zach401/Solaris_MPPT/Electrical Hardware/BoardReference.png

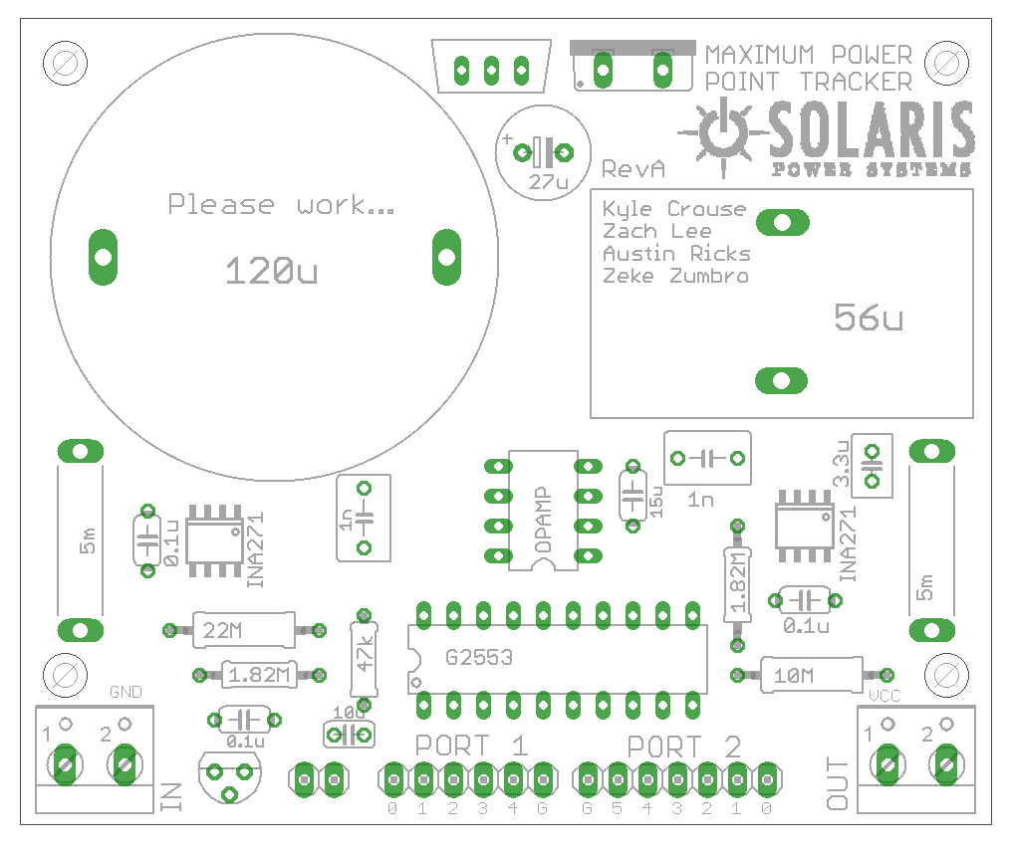
Electrical Hardware/BoardReference.png
