zach401/Solaris_MPPT/Electrical Hardware/DC-DC Converter/DC-DC Schem.PNG

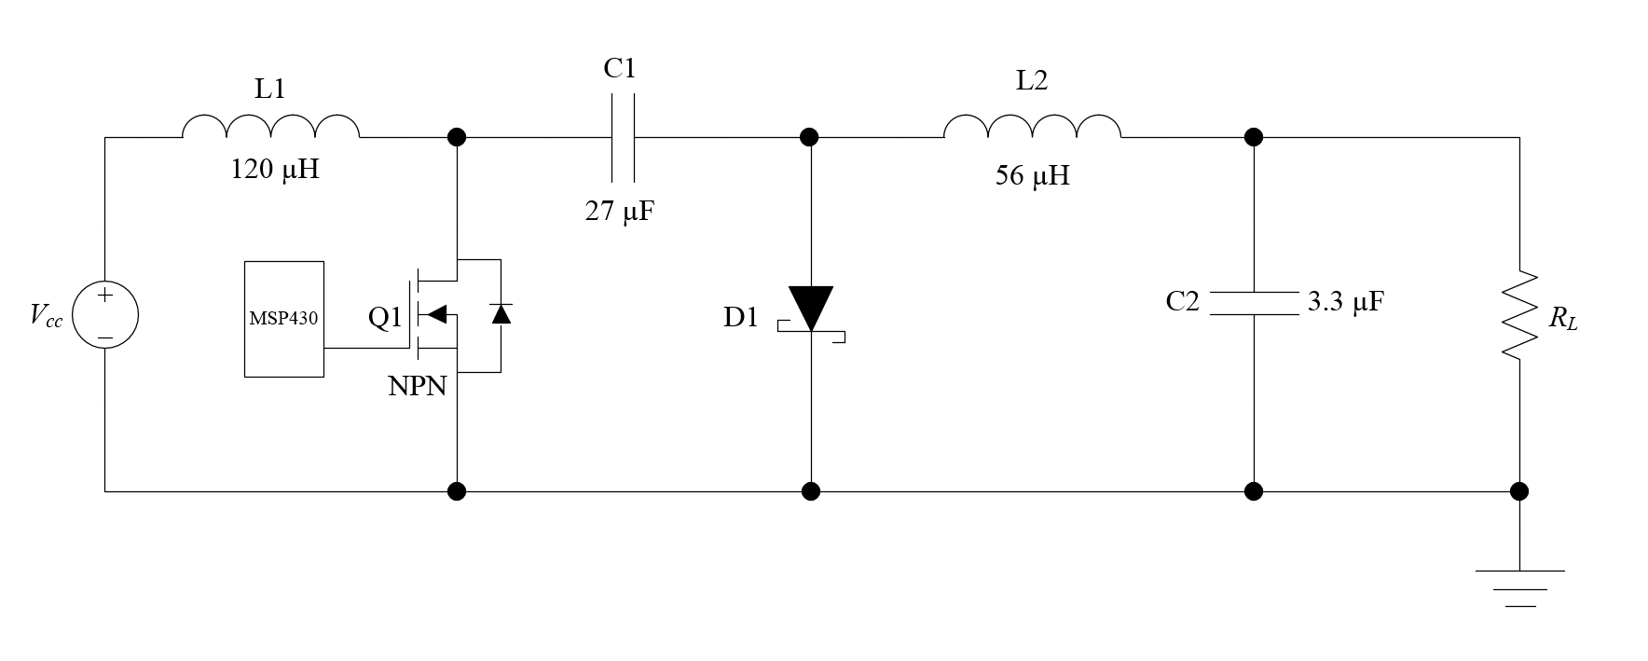
Electrical Hardware/DC-DC Converter/DC-DC Schem.PNG
