zach401/Solaris_MPPT/Electrical Hardware/EAGLE/Capture.PNG

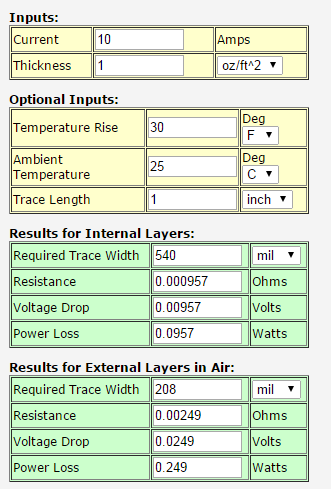
Electrical Hardware/EAGLE/Capture.PNG
