zach401/Solaris_MPPT/Electrical Hardware/Schematic.tif

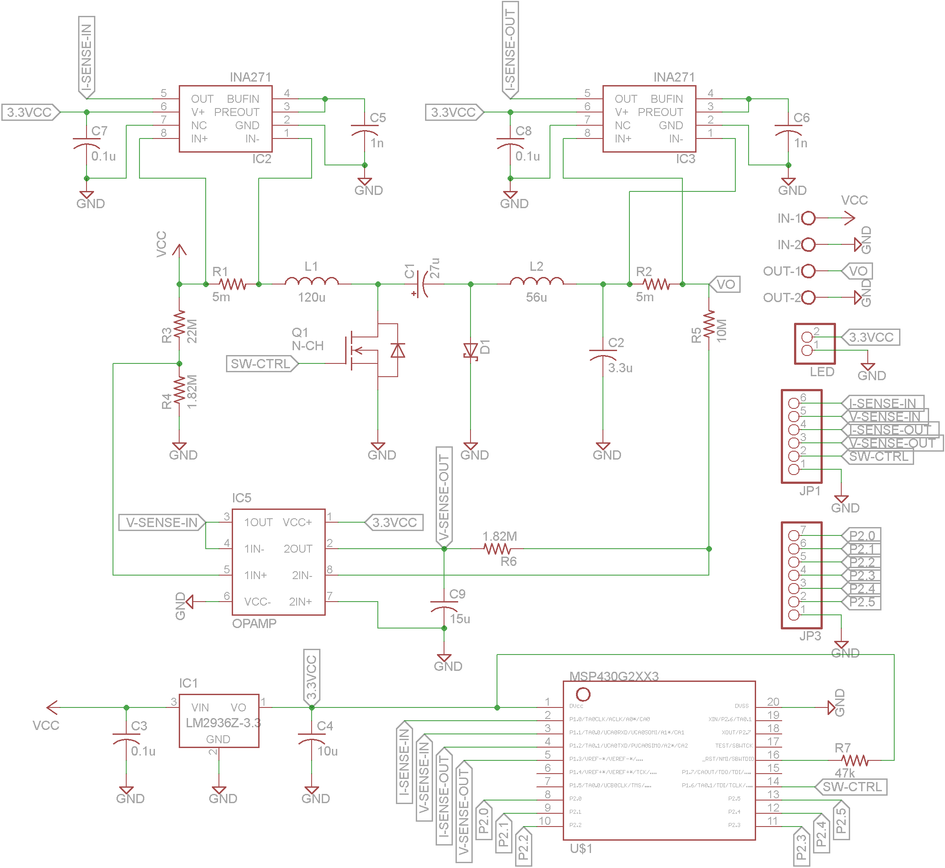
Electrical Hardware/Schematic.tif
