zach401/Solaris_MPPT/Mechanical Hardware/Gland2.png

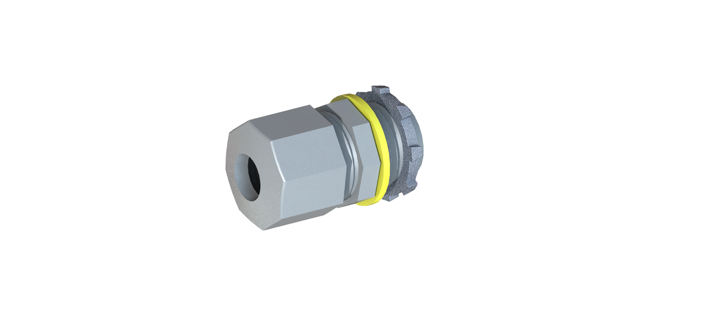
Mechanical Hardware/Gland2.png
