zach401/Solaris_MPPT/Mechanical Hardware/MKIwithoutLid.png

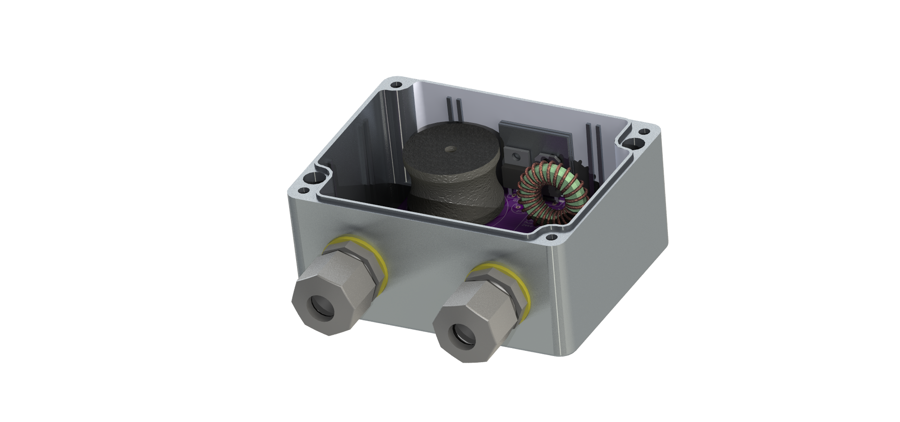
Mechanical Hardware/MKIwithoutLid.png
