zach401/Solaris_MPPT/Prototype Pictures, Videos/photo 1.JPG

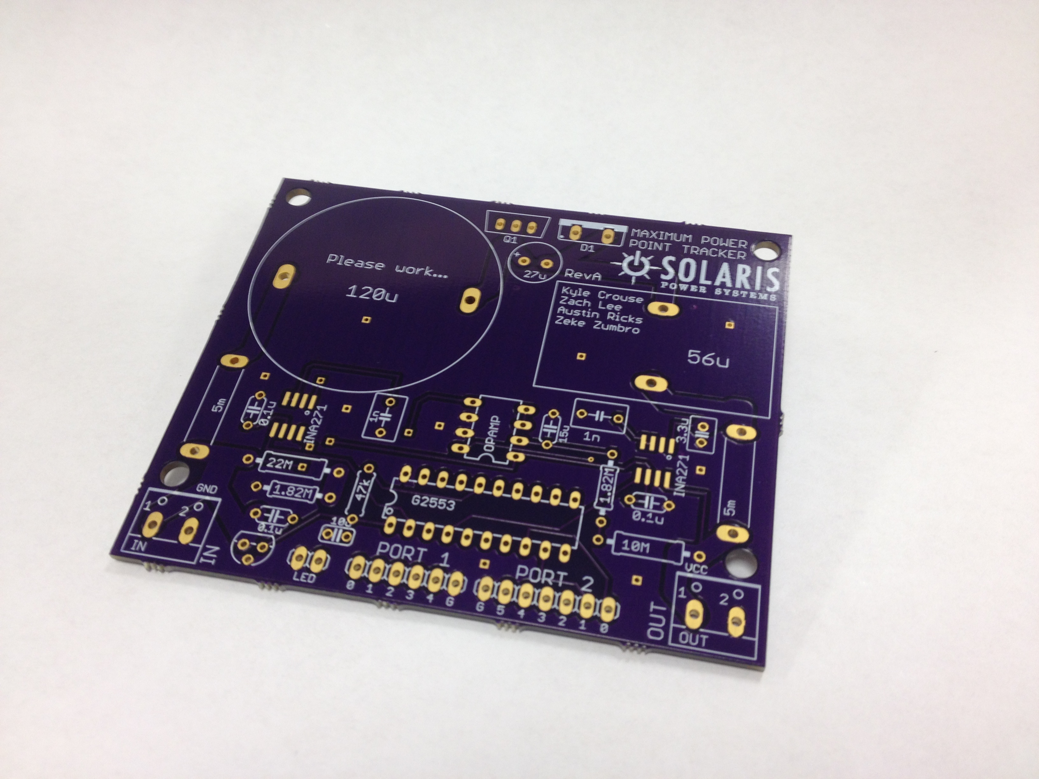
Prototype Pictures, Videos/photo 1.JPG
