zach401/Solaris_MPPT/Prototype Pictures, Videos/photo 2.JPG

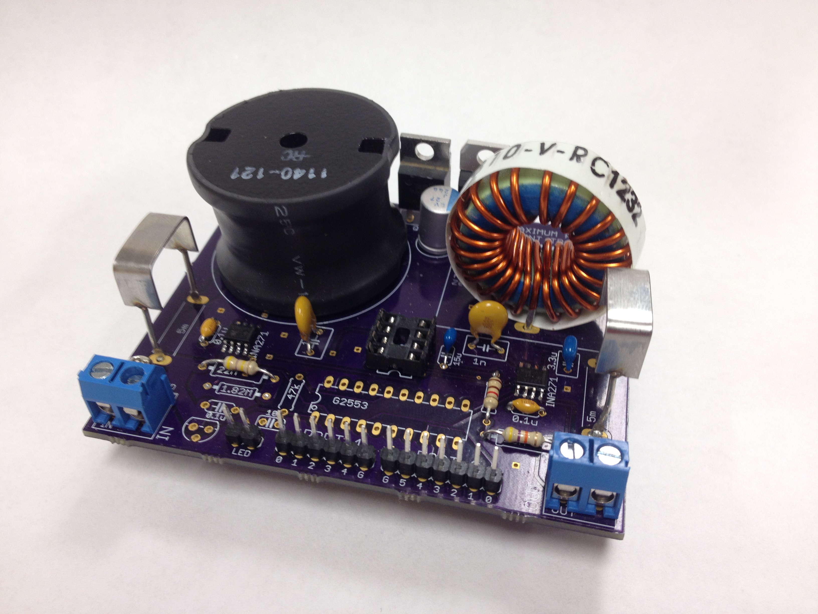
Prototype Pictures, Videos/photo 2.JPG
