zach401/Solaris_MPPT/Prototype Pictures, Videos/photo.JPG

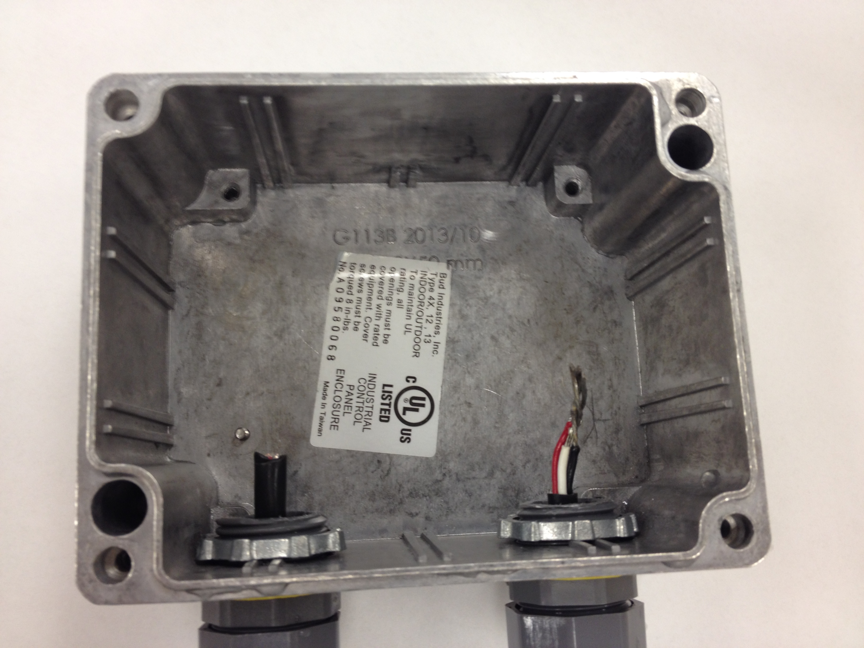
Prototype Pictures, Videos/photo.JPG
