zach401/Solaris_MPPT/Prototype Pictures, Videos/Product.PNG

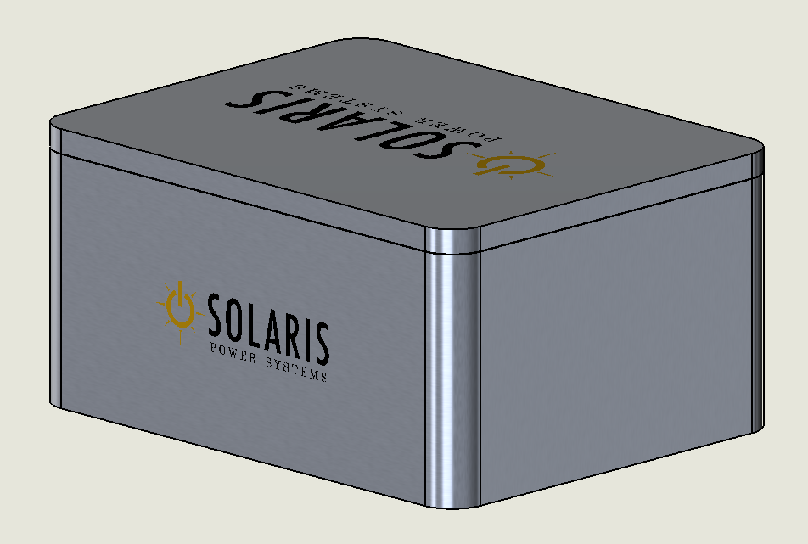
Prototype Pictures, Videos/Product.PNG
