zach401/Solaris_MPPT/Mechanical Hardware/VariousComponents/BottomScrew.SLDPRT

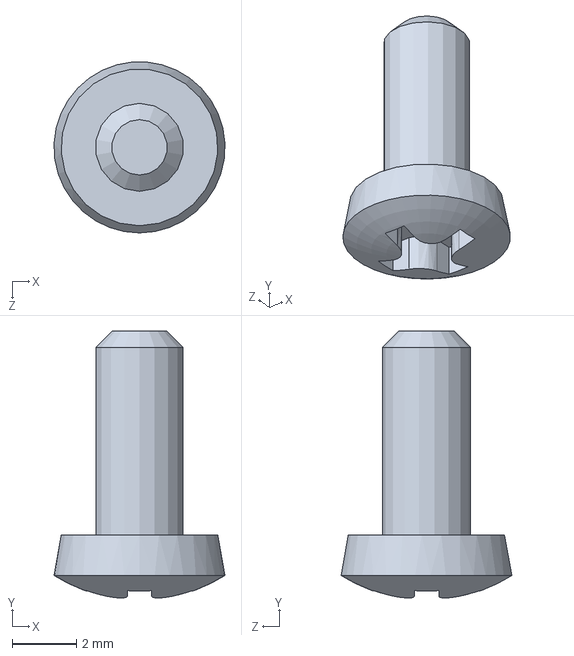
[picture p55: CAD file, 2015-09-25]
Mechanical Hardware/VariousComponents/BottomScrew.SLDPRT
5.33 x 8.32 x 5.32 mm
