zach401/Solaris_MPPT/Mechanical Hardware/CableGland/GlandRubberWasher.SLDPRT

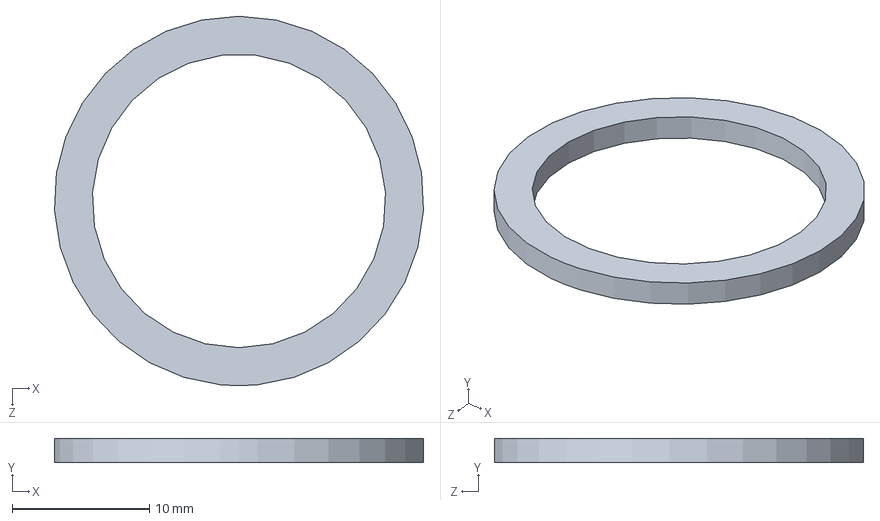
[picture p56: CAD file, 2015-09-25]
Mechanical Hardware/CableGland/GlandRubberWasher.SLDPRT
26.9 x 1.78 x 26.9 mm
