zach401/Solaris_MPPT/LTSPICE/cuk_converter2.asc

C1: cap; 27µ
C2: cap; 3.3µ
C3: cap; 15µ
D1: schottky; PDS5100
L1: ind; 120µ
L2: ind; 56µ
M1: nmos; IRFH5250
R1: res; 10
R2: res; 10e3
R3: res; 1.8e3
R4: res; 20e4
R5: res; 1.8e4
R6: res; 5m
R7: res; 5m
U1: LT1630
U2: LT1630
V1: voltage; {Vs}
V2: voltage; PULSE(0 3.3 0 1n 1n {DT} 5u)
V3: voltage; 3.3
Named nets: 0
.tran 0 10m 1m
.param DT = {(((Vset / (Vs + Vset) ) * 5)*1e-6)}
.param Vs 38
.param Vset = 10
